philibus-coder/Drawfinity/IMG_7286.JPG

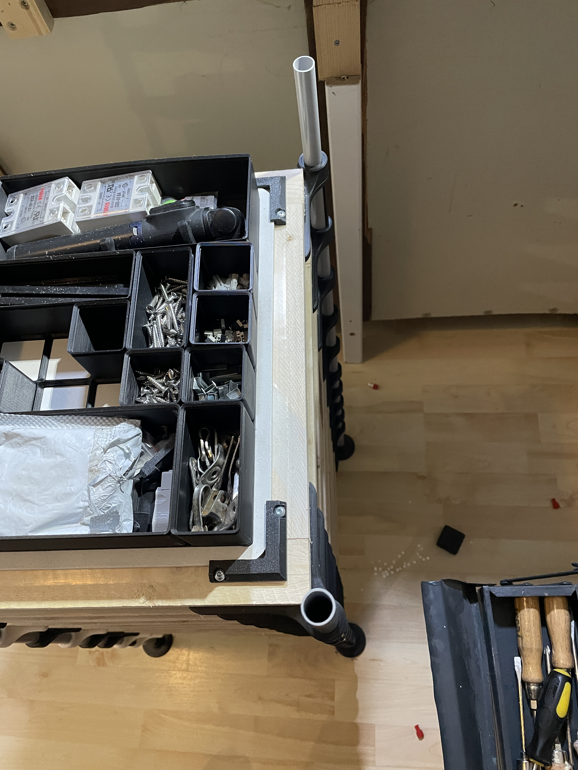
IMG_7286.JPG
